ekumanov/cybrid/img/IMG_0277.jpeg

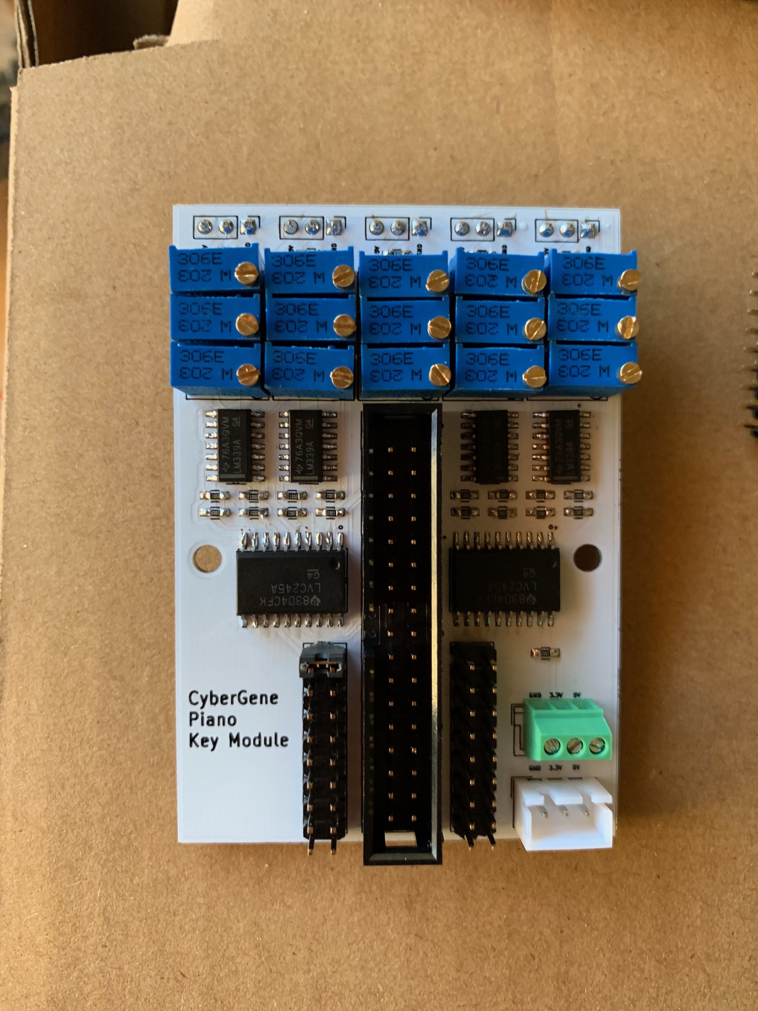
img/IMG_0277.jpeg
