ekumanov/cybrid/img/IMG_1386.jpeg

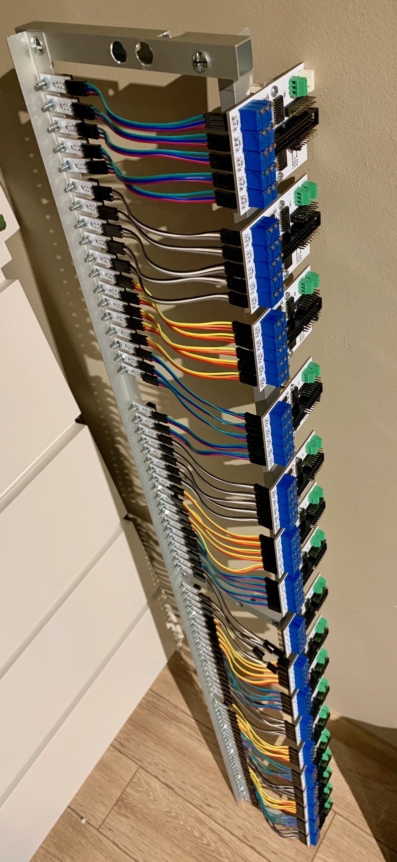
img/IMG_1386.jpeg
