ekumanov/cybrid/img/IMG_1389.jpeg

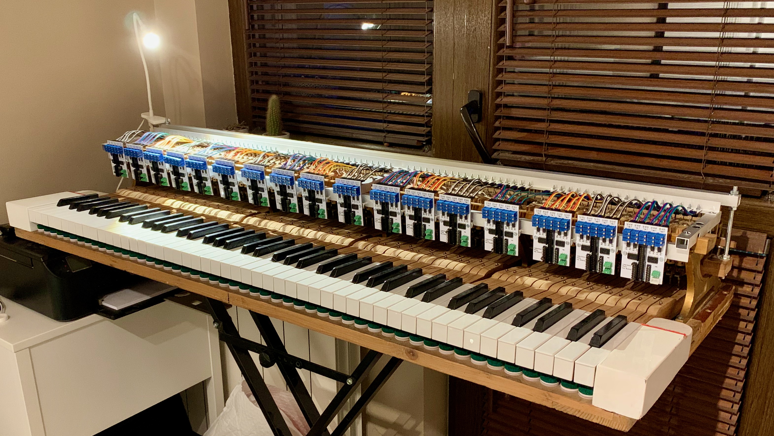
img/IMG_1389.jpeg
