ekumanov/cybrid/img/IMG_1390.jpeg

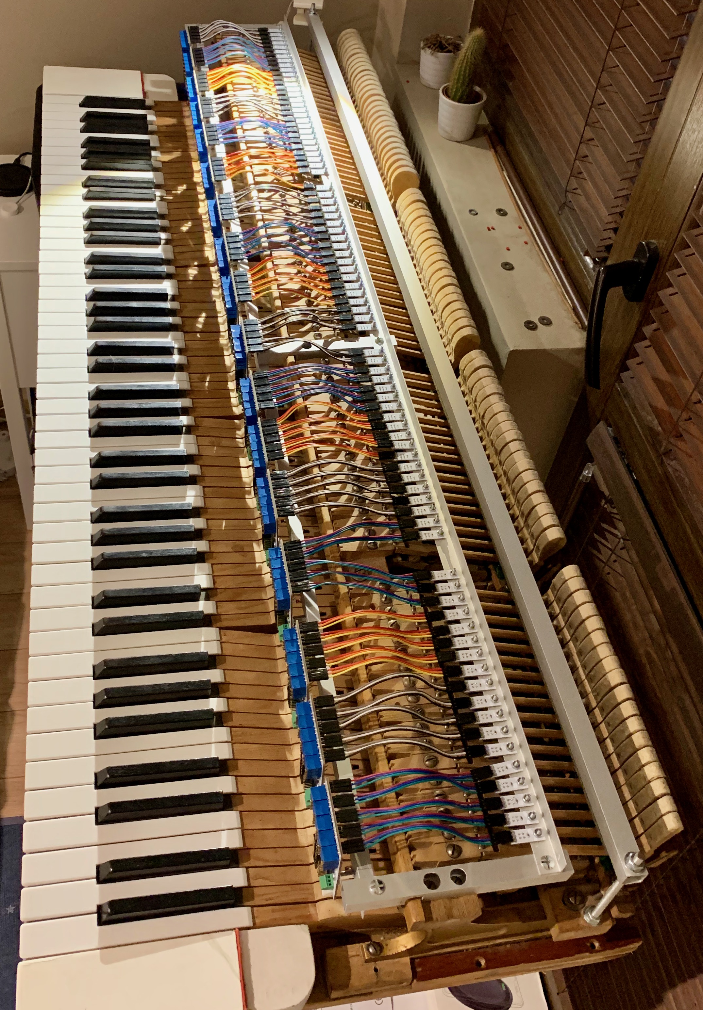
img/IMG_1390.jpeg
