ekumanov/cybrid/img/IMG_1409.jpeg

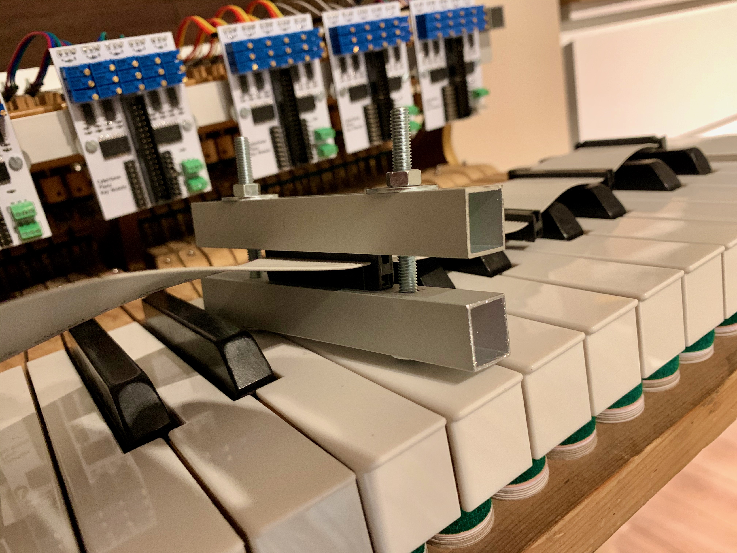
img/IMG_1409.jpeg
