ekumanov/cybrid/img/IMG_1519.jpeg

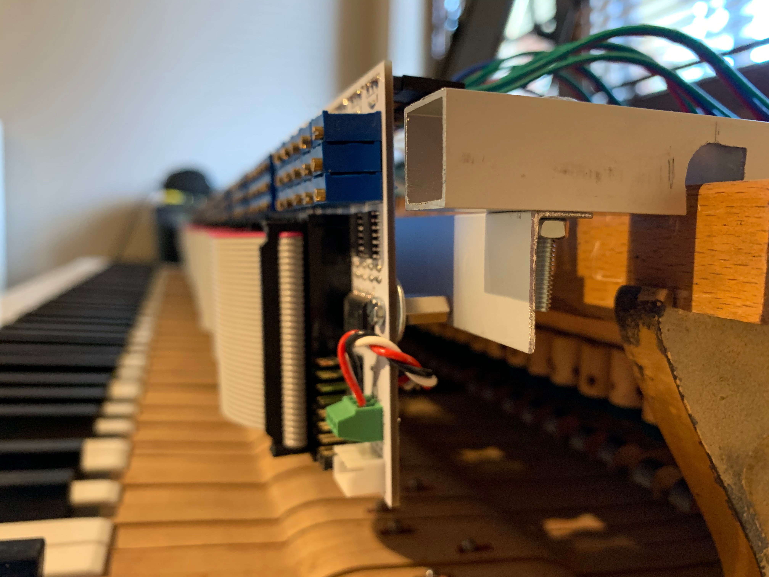
img/IMG_1519.jpeg
