ekumanov/cybrid/img/IMG_1520.jpeg

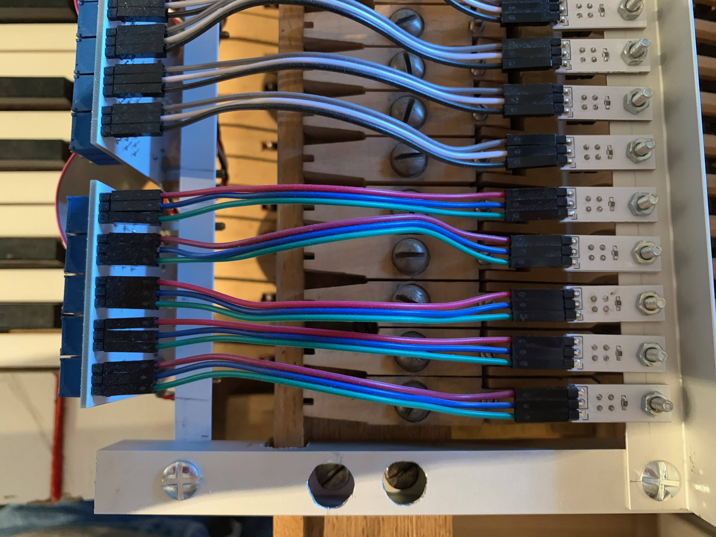
img/IMG_1520.jpeg
