ekumanov/cybrid/img/IMG_1521.jpeg

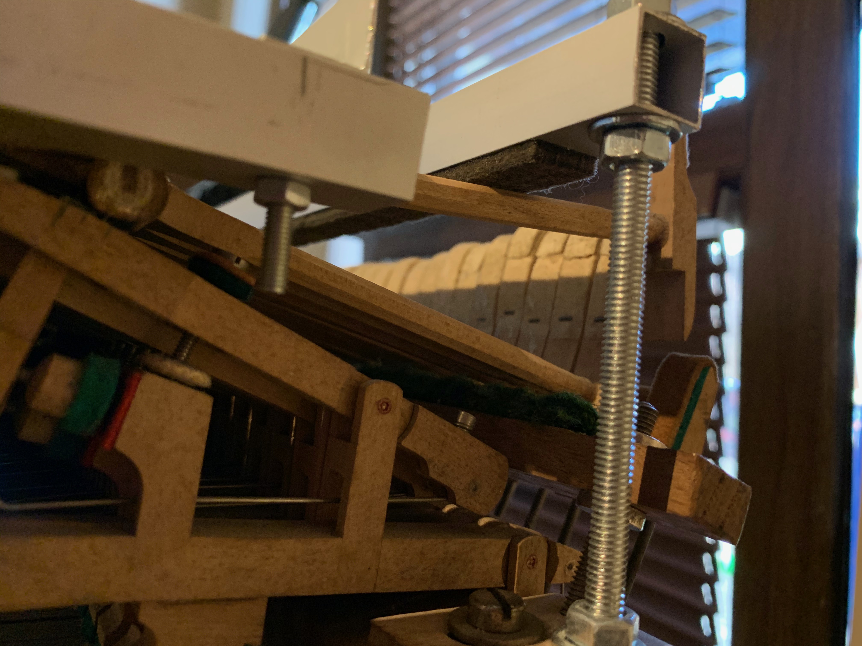
img/IMG_1521.jpeg
