ekumanov/cybrid/img/IMG_1522.jpeg

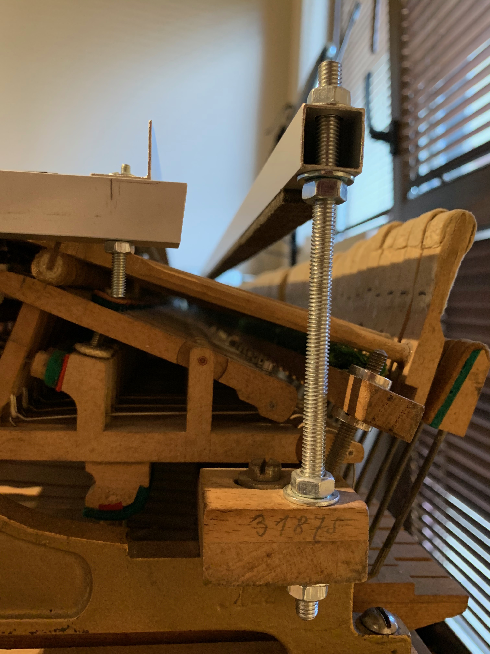
img/IMG_1522.jpeg
