ekumanov/cybrid/img/IMG_1527.jpeg

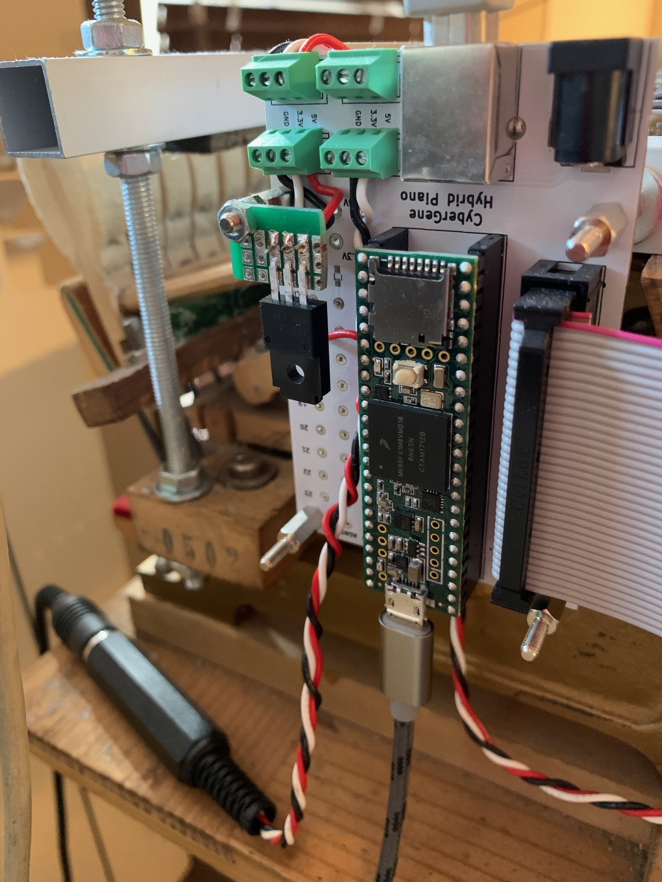
img/IMG_1527.jpeg
