ekumanov/cybrid/img/IMG_1528.jpeg

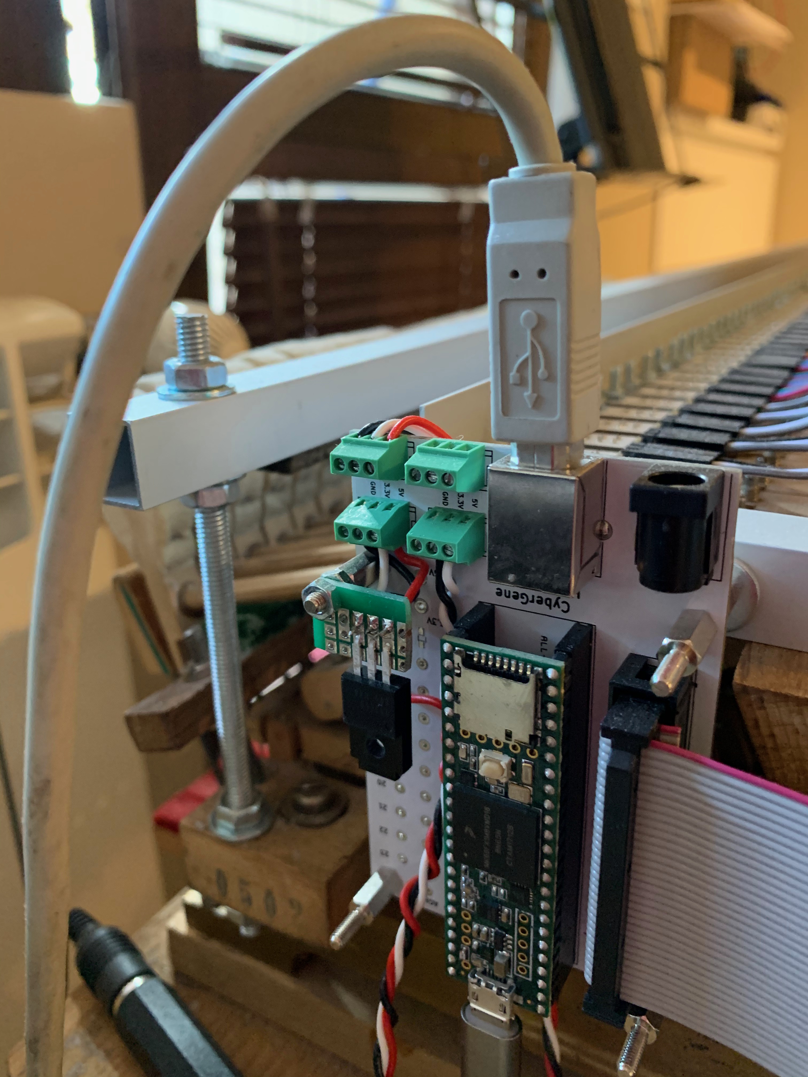
img/IMG_1528.jpeg
