ekumanov/cybrid/img/IMG_1530.jpeg

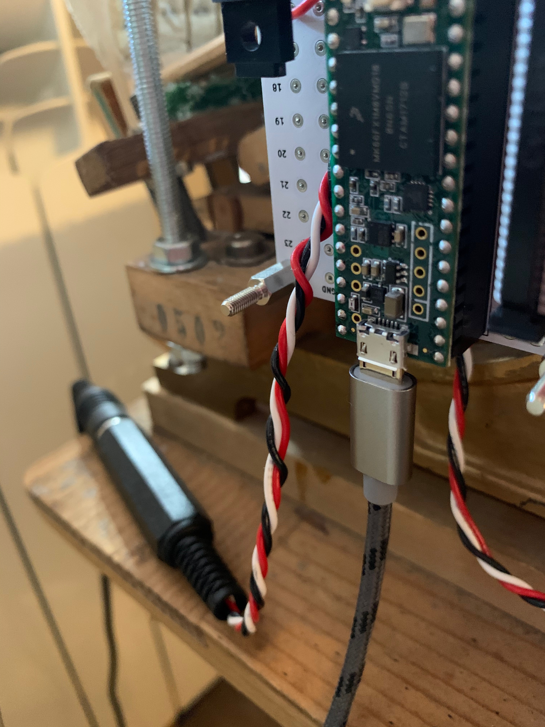
img/IMG_1530.jpeg
