ekumanov/cybrid/img/IMG_1531.jpeg

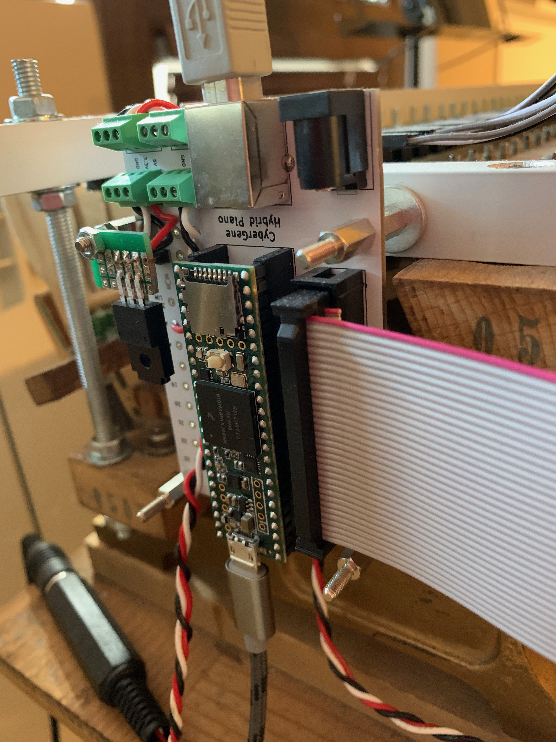
img/IMG_1531.jpeg
