ekumanov/cybrid/img/IMG_1532.jpeg

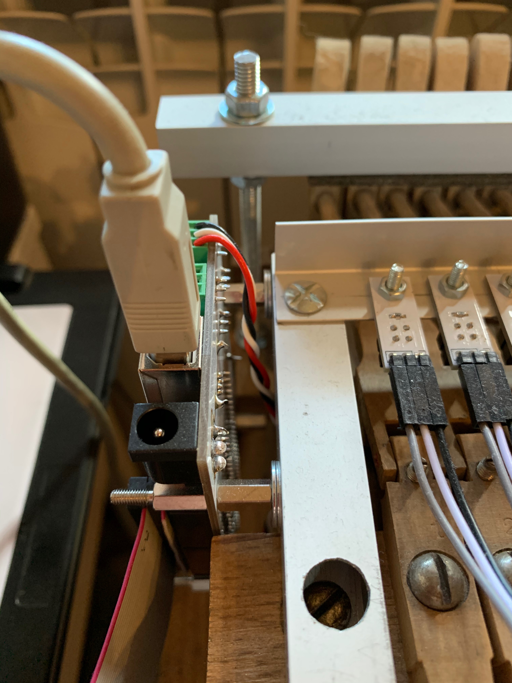
img/IMG_1532.jpeg
